PrinceYadav78/My_custom_miner/img/1.png

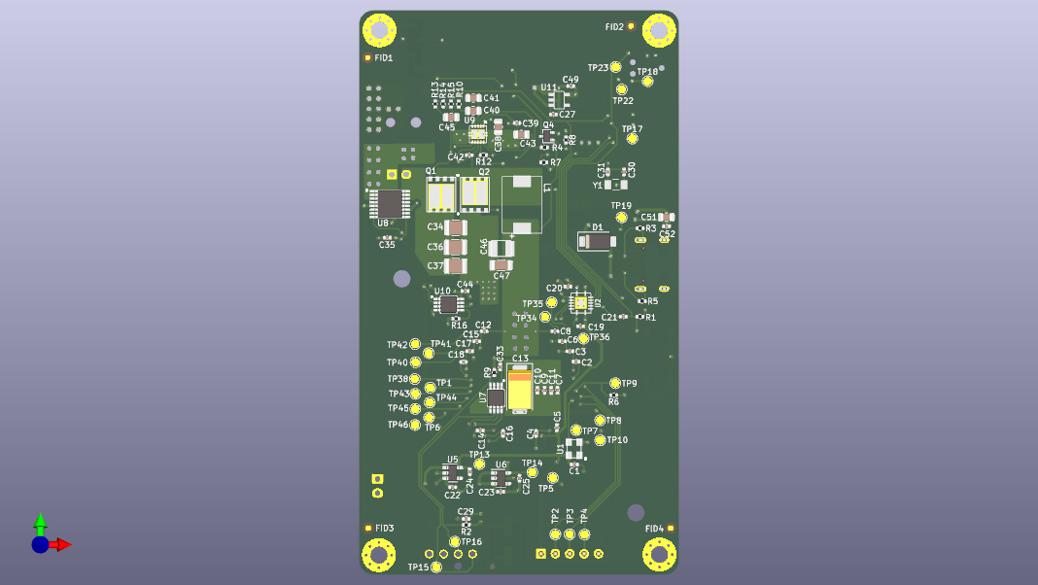
img/1.png
