PrinceYadav78/My_custom_miner/img/3.png

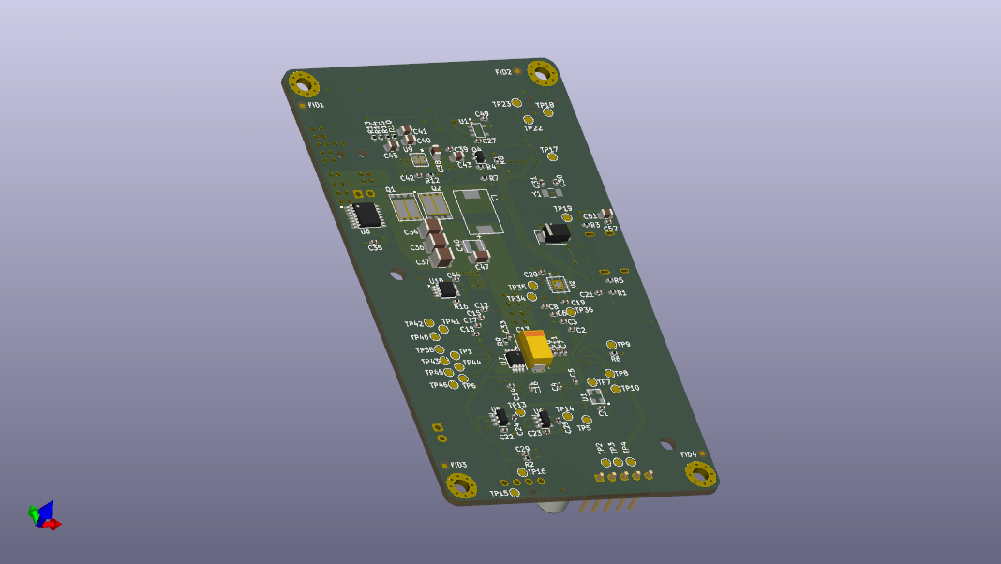
img/3.png
