PrinceYadav78/My_custom_miner/img/4.png

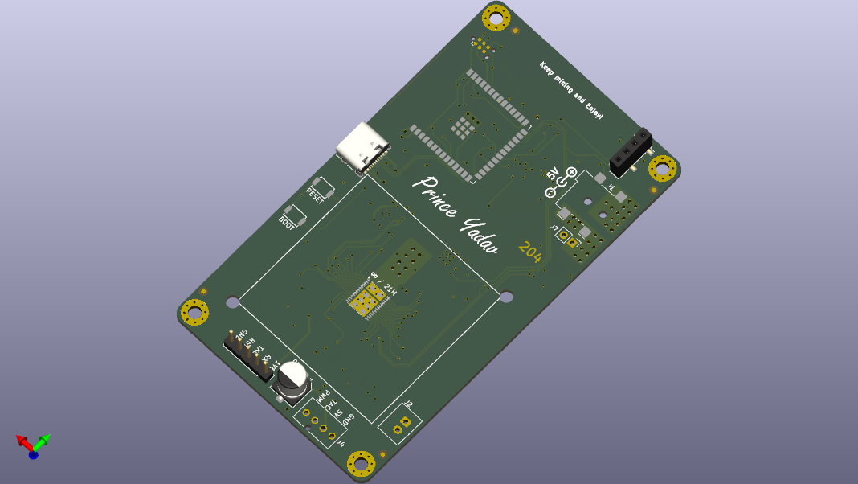
img/4.png
