PrinceYadav78/My_custom_miner/img/Screenshot 2026-01-02 192252.png

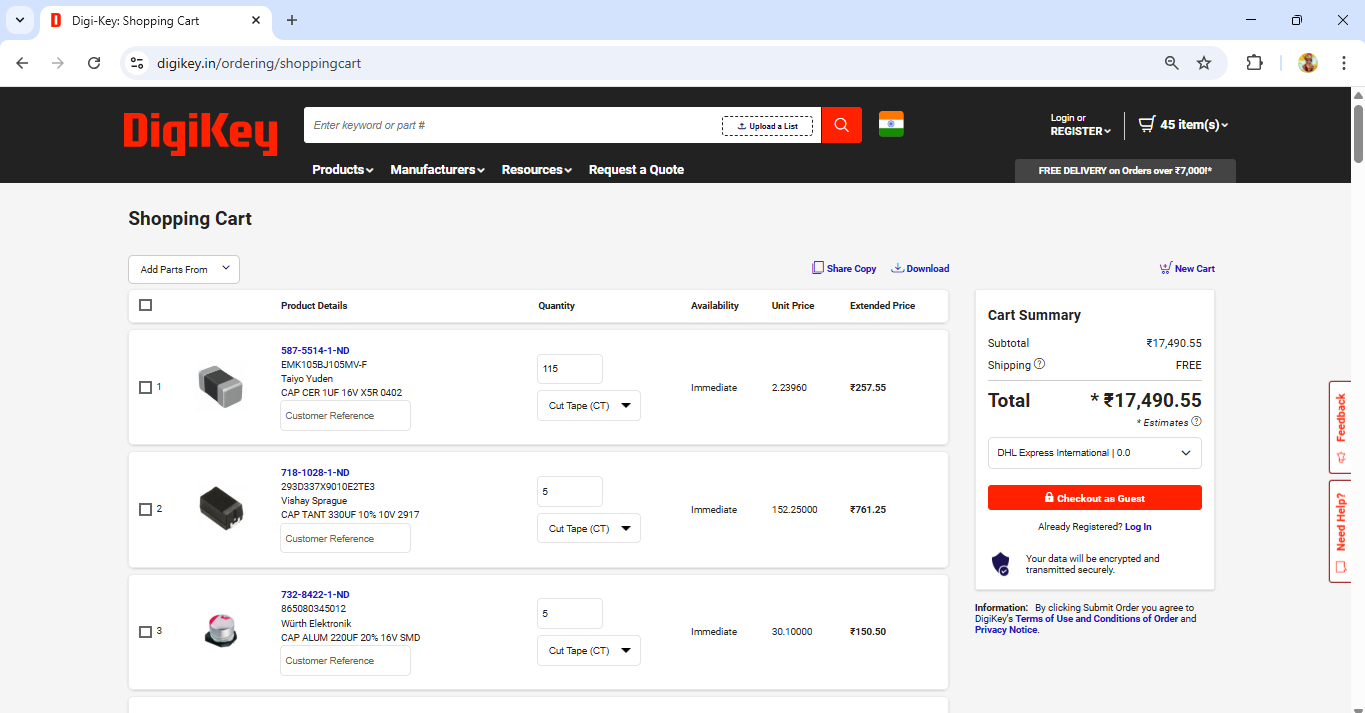
img/Screenshot 2026-01-02 192252.png
