PrinceYadav78/My_custom_miner/img/Screenshot 2026-01-02 192635.png

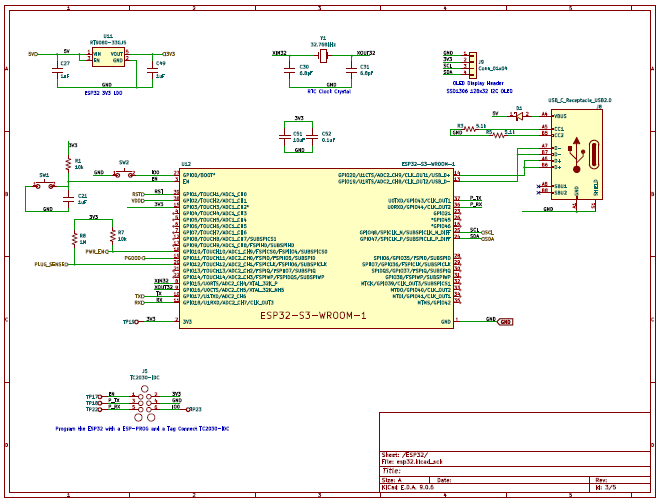
img/Screenshot 2026-01-02 192635.png
